matiasmicheletto/fpv-rover/img/pic_1.jpg

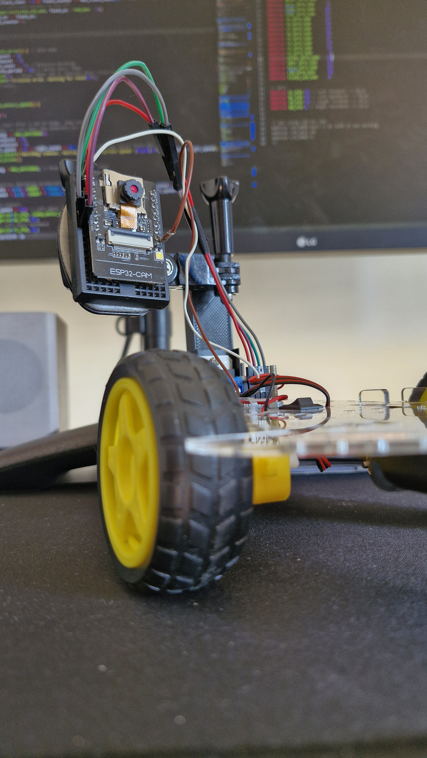
img/pic_1.jpg
