matiasmicheletto/fpv-rover/img/pic_2.jpg

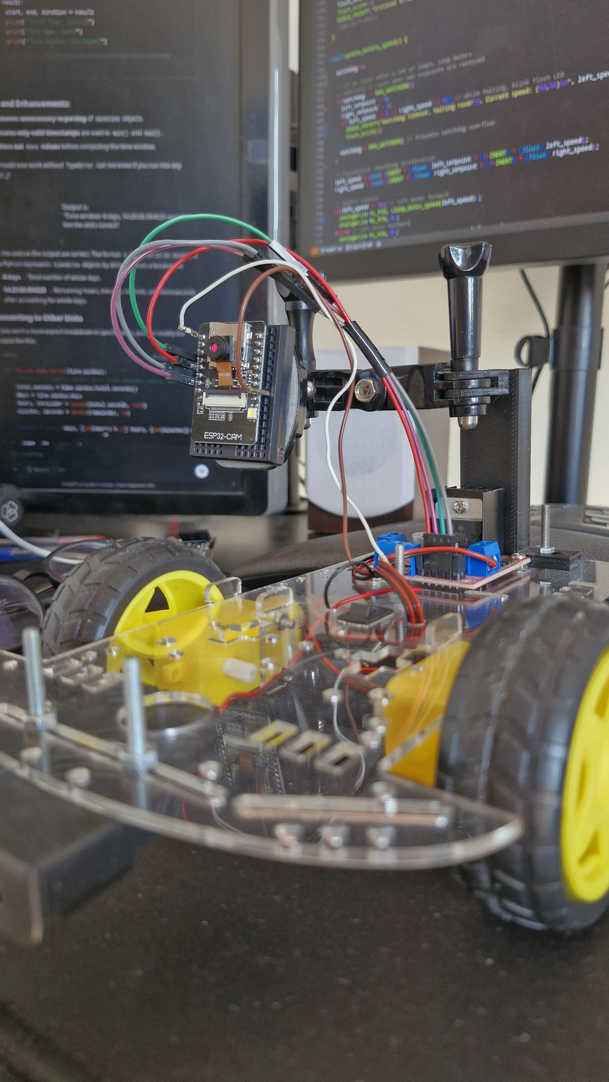
img/pic_2.jpg
