matiasmicheletto/fpv-rover/img/screenshot.png

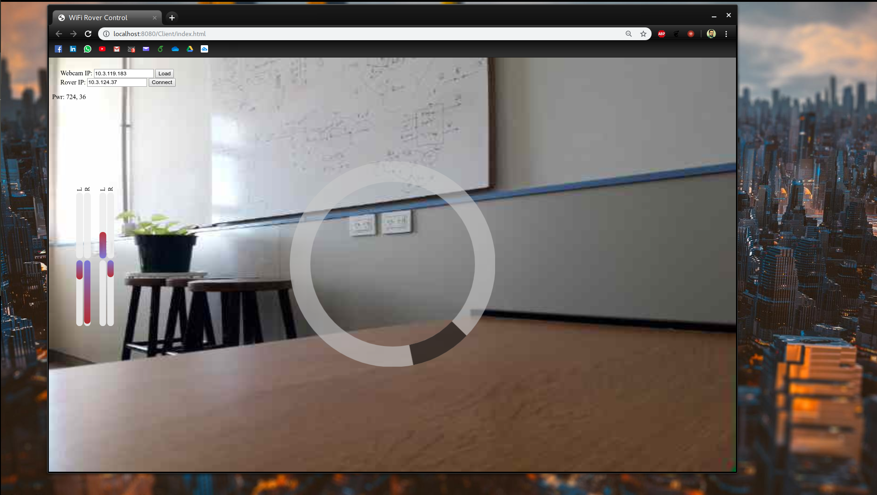
img/screenshot.png
