matiasmicheletto/fpv-rover/img/v1-assembling/Assembling_0.jpg

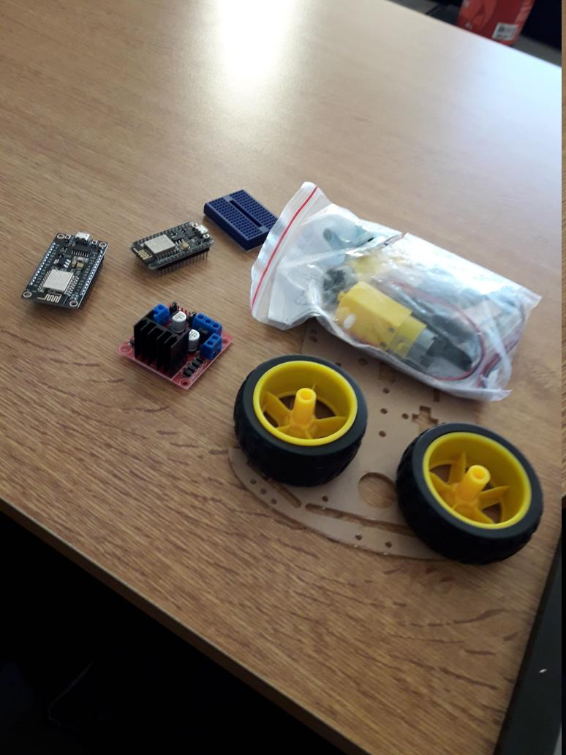
img/v1-assembling/Assembling_0.jpg
