matiasmicheletto/fpv-rover/img/v1-assembling/Assembling_1.jpg

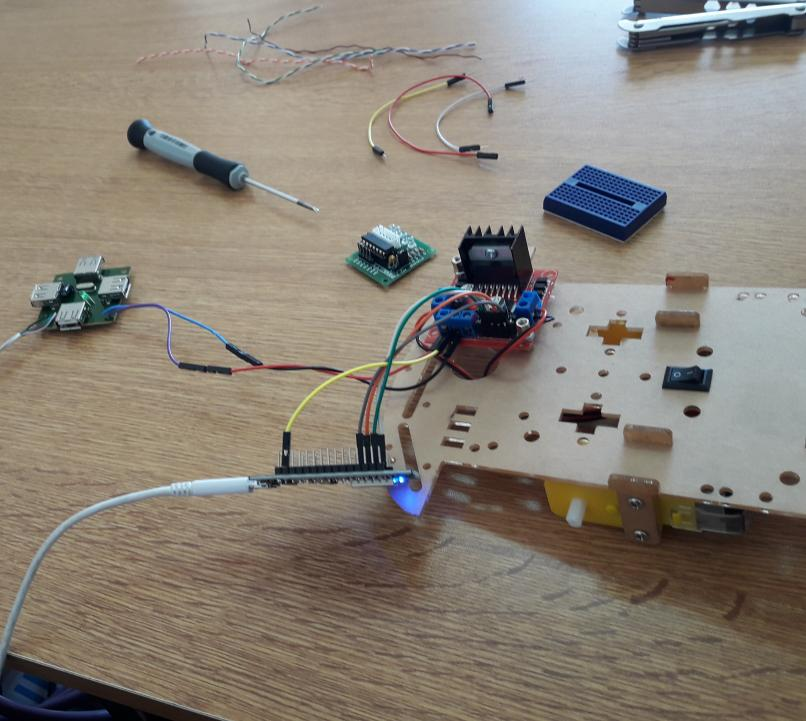
img/v1-assembling/Assembling_1.jpg
