matiasmicheletto/fpv-rover/img/v1-assembling/Assembling_4.jpg

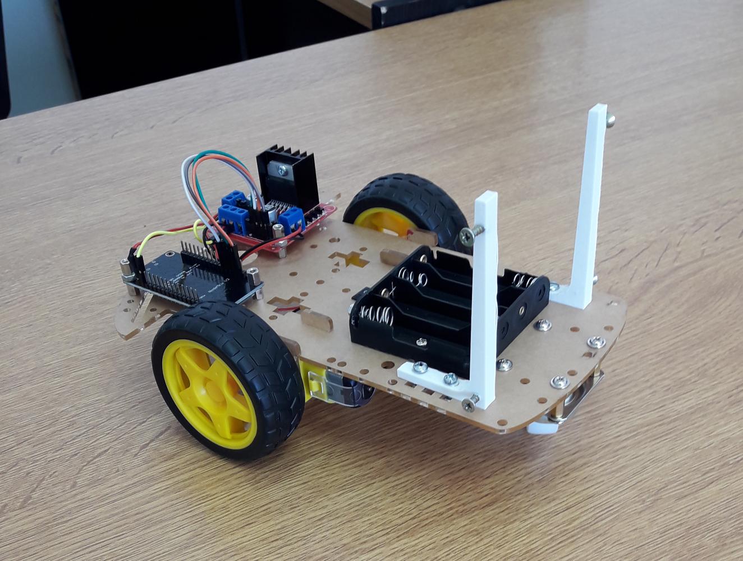
img/v1-assembling/Assembling_4.jpg
