matiasmicheletto/fpv-rover/img/v1-assembling/Assembling_5.jpg

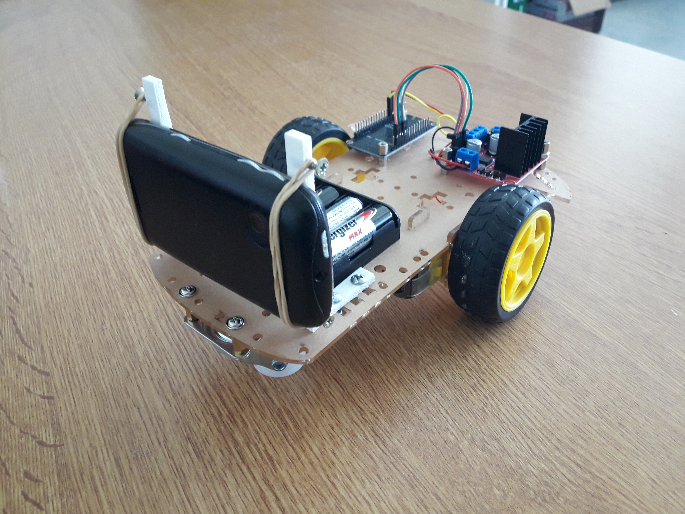
img/v1-assembling/Assembling_5.jpg
